patagonaa/solar-system/img/01_battery/02_bms-corroded.jpg

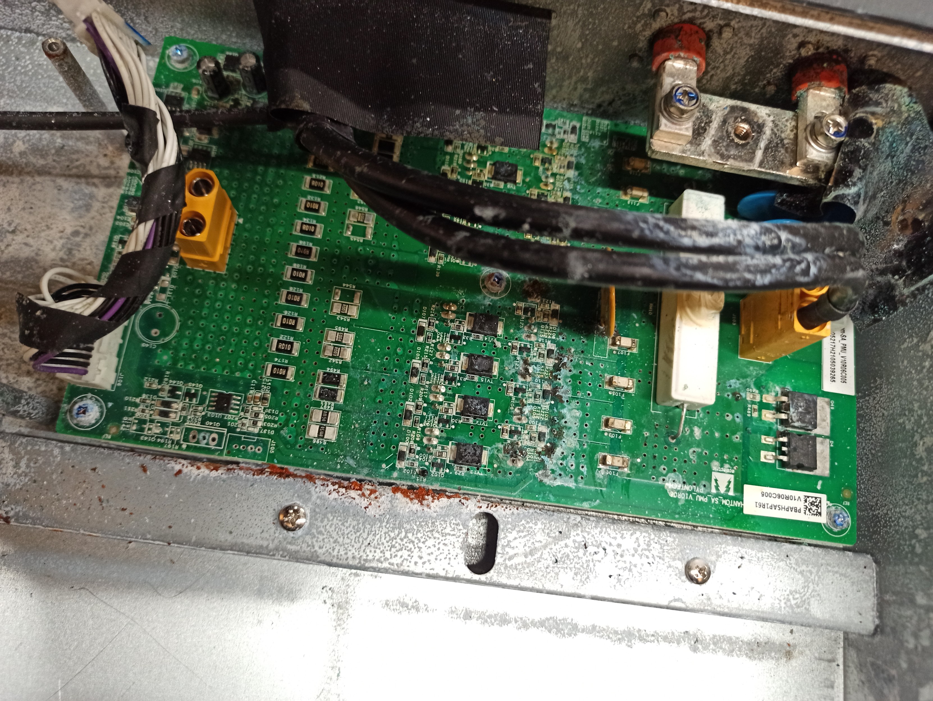
img/01_battery/02_bms-corroded.jpg
