patagonaa/solar-system/img/01_battery/04_bms-corroded.jpg

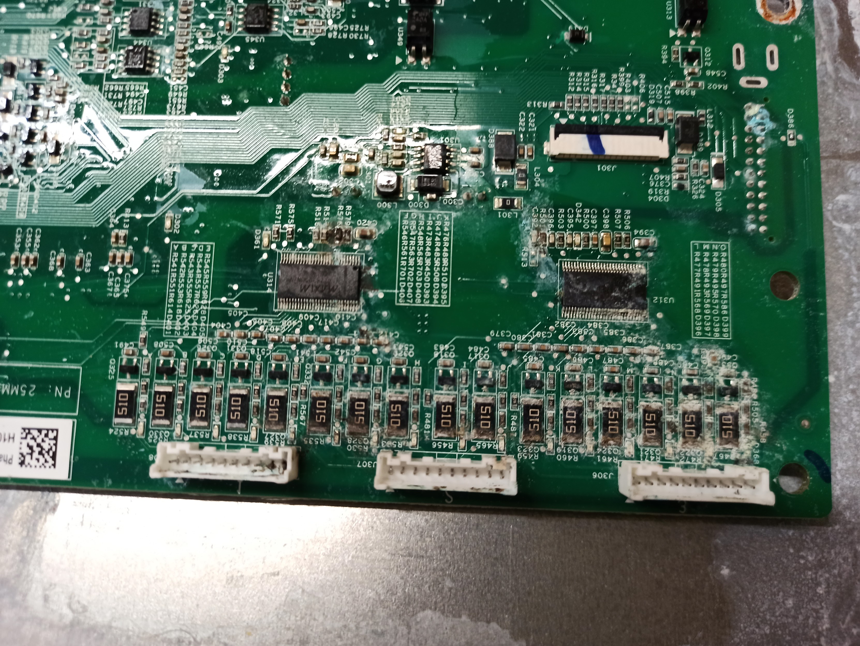
img/01_battery/04_bms-corroded.jpg
