patagonaa/solar-system/img/01_battery/04_cell-pack.jpeg

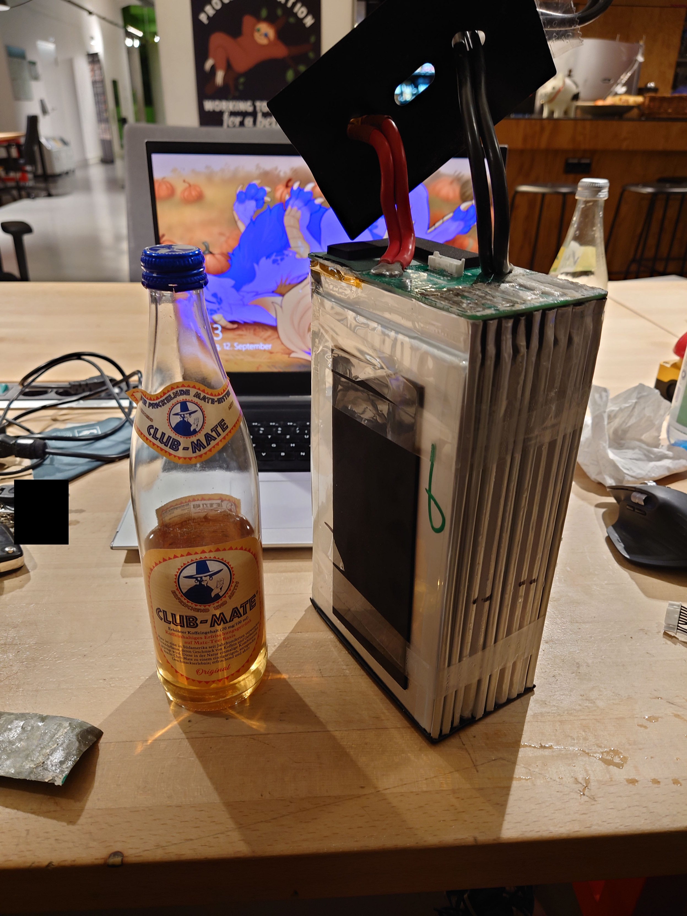
img/01_battery/04_cell-pack.jpeg
