patagonaa/solar-system/img/01_battery/05_cell-pack.jpeg

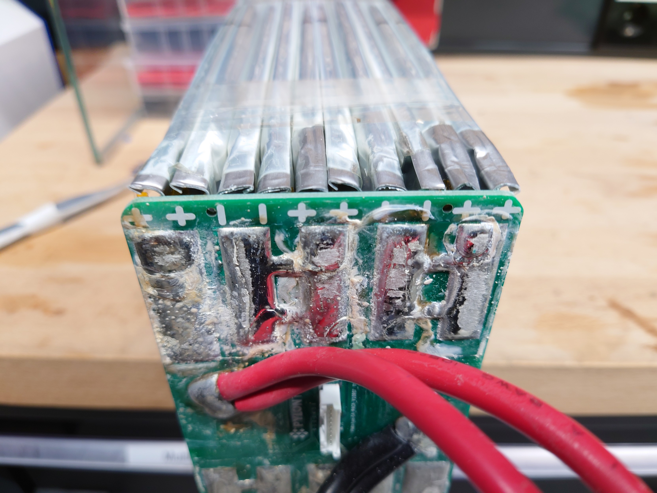
img/01_battery/05_cell-pack.jpeg
