patagonaa/solar-system/img/01_battery/07_battery-charging.jpg

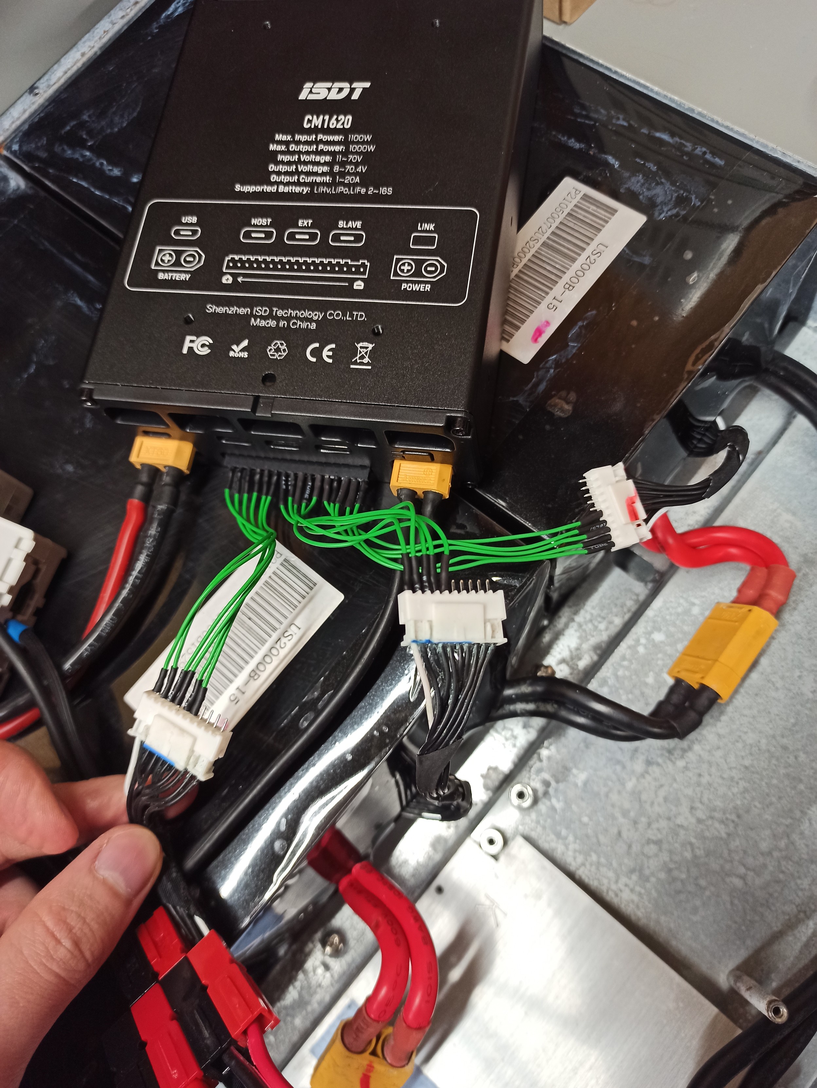
img/01_battery/07_battery-charging.jpg
