patagonaa/solar-system/img/01_battery/08_battery-charging.jpg

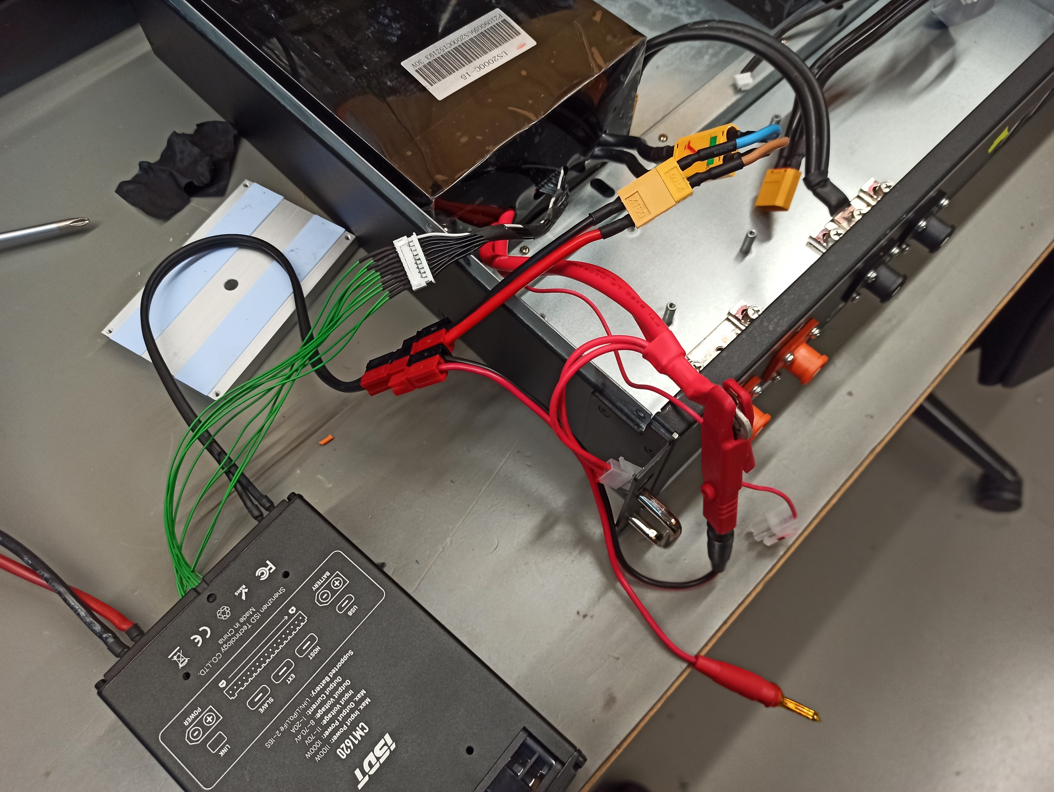
img/01_battery/08_battery-charging.jpg
