patagonaa/solar-system/img/02_bms/01_bms-wires.jpg

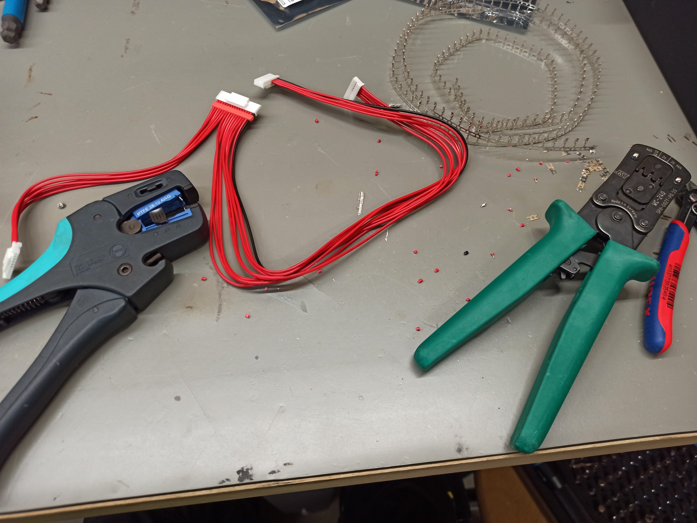
img/02_bms/01_bms-wires.jpg
