patagonaa/solar-system/img/02_bms/04_bms-mounted.jpg

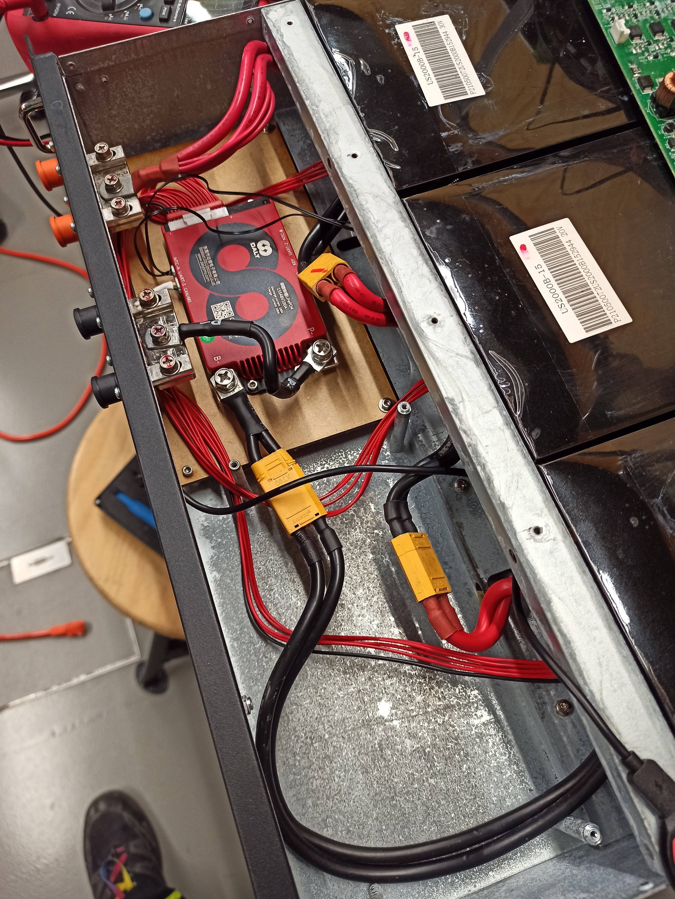
img/02_bms/04_bms-mounted.jpg
