patagonaa/solar-system/cad/inverter-box/frontpanel/mount_sb120.stl

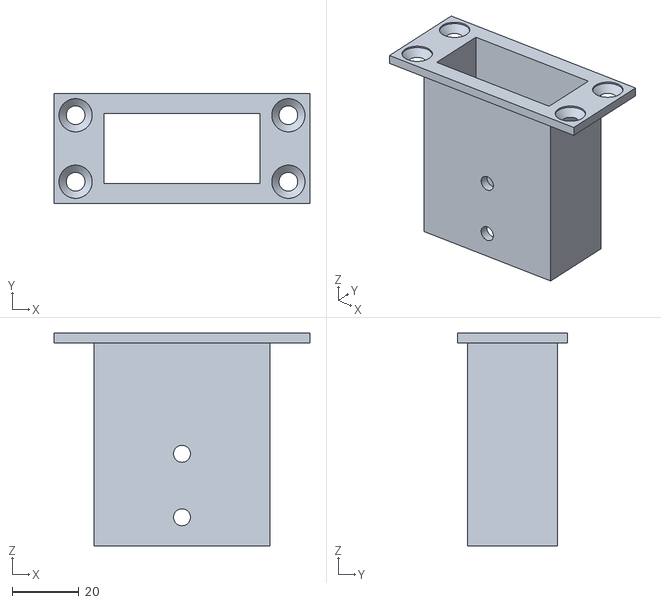
[picture p45: CAD file, 2025-01-11]
cad/inverter-box/frontpanel/mount_sb120.stl
77.0 x 33.0 x 64.0
