patagonaa/solar-system/cad/inverter-box/frontpanel/din-rail-mount.stl

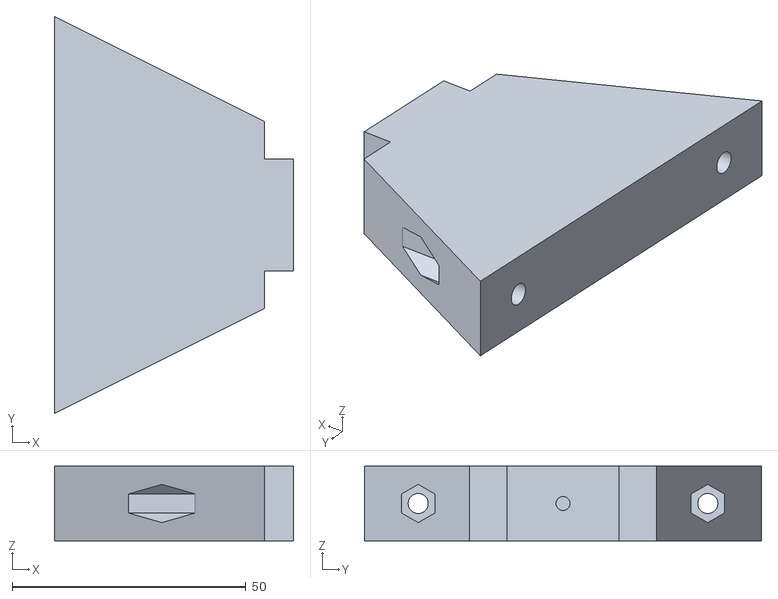
[picture p46: CAD file, 2025-01-09]
cad/inverter-box/frontpanel/din-rail-mount.stl
51.2 x 85.0 x 16.0
