patagonaa/solar-system/cad/esp-box/esp32-case.stl

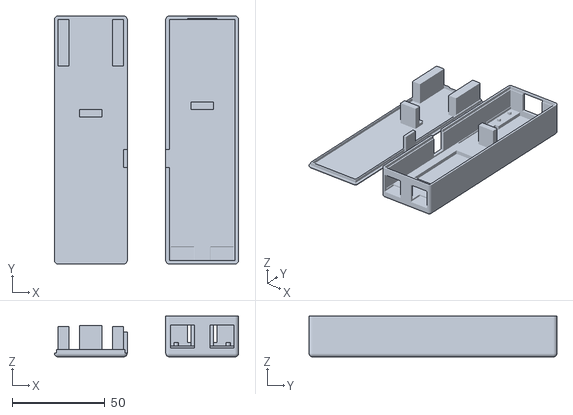
[picture p47: CAD file, 2025-01-19, an earlier design]
cad/esp-box/esp32-case.stl
99.3 x 133.6 x 22.0
